lucaskkergg/proj_int_1_sem_2020_grupo_d_manut/Documentos/AULA-04-TORÇÃO.pdf

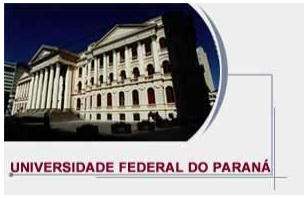
[picture p108: figure]

# TORÇÃO

Prof. Dr. Carlos A. Nadal

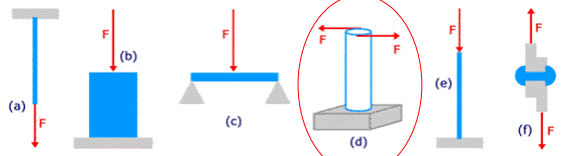
[picture p109: figure]

Tipo de esforços
a) Tração
b) Compressão
c) Flexão
d) Torção
e) Compressão
f) flambagem

Esforços axiais

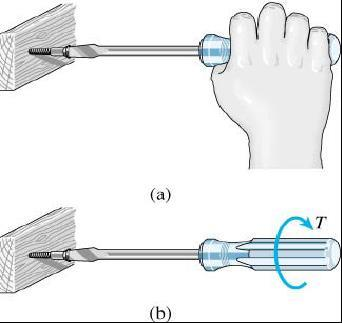
[picture p110: figure]

existe uma torção quando
uma seção transversal de
uma peça está sob a ação
de um conjugado que
tende a torce-la.

O plano de ação do conjugado = plano da seção transversal.
Os conjugados são chamados de momentos de torção, momentos torcionais ou torque T , ' T , e que têm a mesma intensidade T e sentidos opostos (Nash,1982).

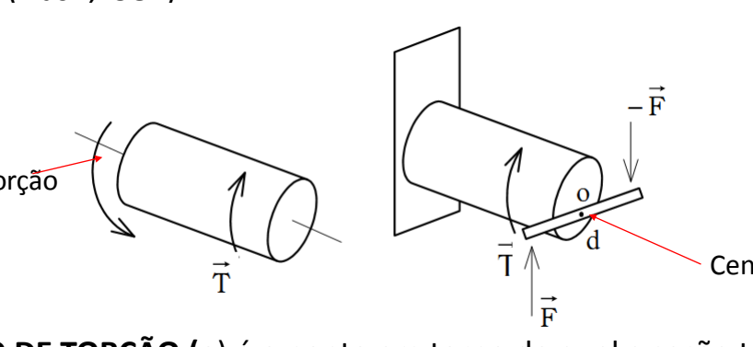
[picture p111: figure]

Centro de torção

Eixo de torção

CENTRO DE TORÇÃO (o) é o ponto em torno do qual a seção transversal gira. Para seções simétricas, coincide como o centro de gravidade.
EIXO DE TORÇÃO é o lugar geométrico dos centros de torção.

DEFORMAÇÕES NOS EIXOS CIRCULARES

Um eixo circular está fixado a um suporte por uma de suas extremidades e aplicando-se à extremidade livre um momento de torção T , o eixo gira, e a seção transversal da extremidade apresenta uma rotação representada pelo ângulo φ , chamado ângulo de torção (Beer and Johnston, 1989).

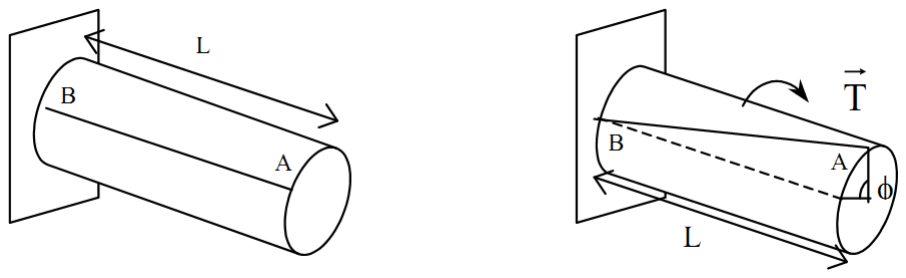
[picture p112: figure]

O ângulo de torção, para uma certa faixa de variação de T, é proporcional tanto a T como ao comprimento do eixo L.
Um prisma de seção circular, tendo uma de suas extremidades fixas, submetido a um momento de torção T.

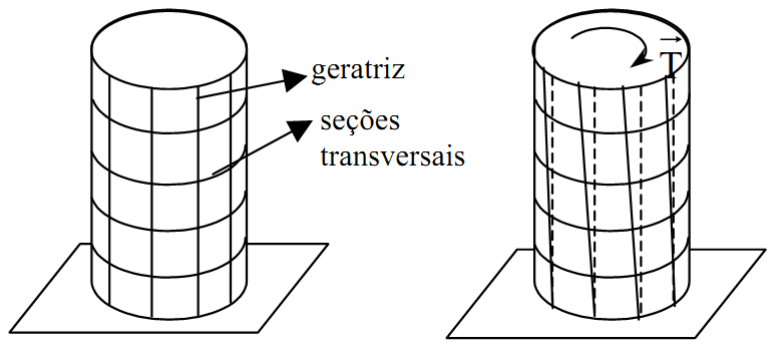
[picture p113: figure]

a) as geratrizes se transformam em hélices;
b) o “quadrado” se transforma em um “losango” com os lados sofrendo a mesma deformação angular;
c) as seções normais permanecem planas e normais ao eixo de rotação e conservam sua forma. Neste caso, é preciso assegurar que os momentos sejam aplicados de tal forma que as extremidades também permaneçam planas sem deformação.

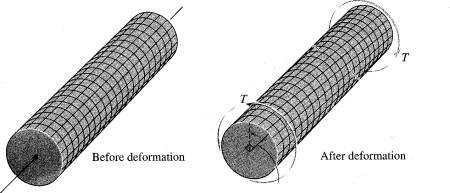
[picture p114: figure]
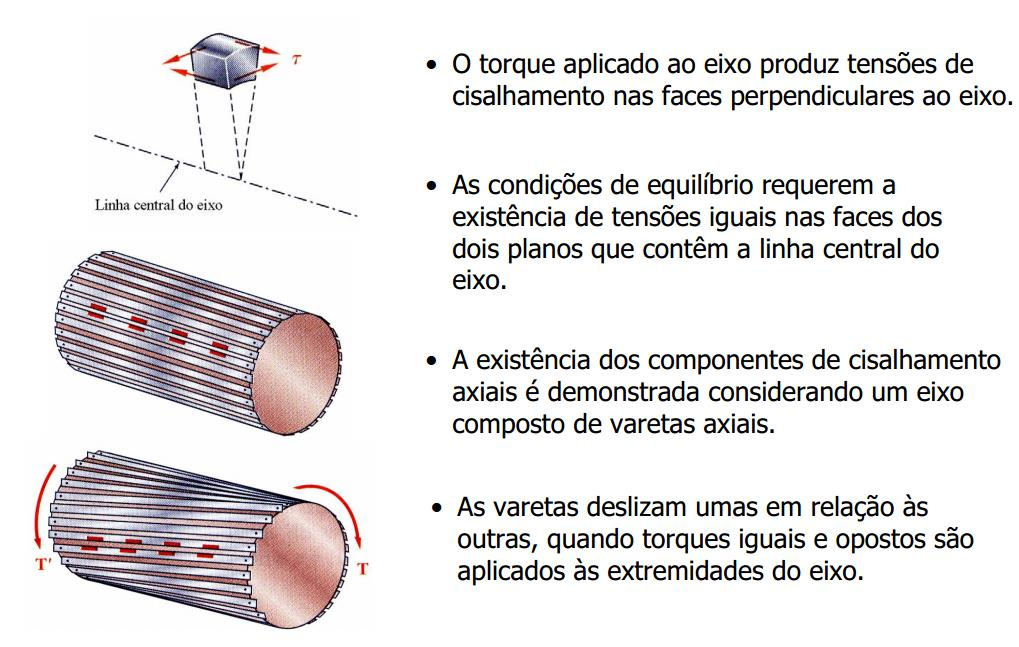
[picture p115: page 8]

Fonte: Prof. Renato Rocha – Resistência dos Materiais - UERJ

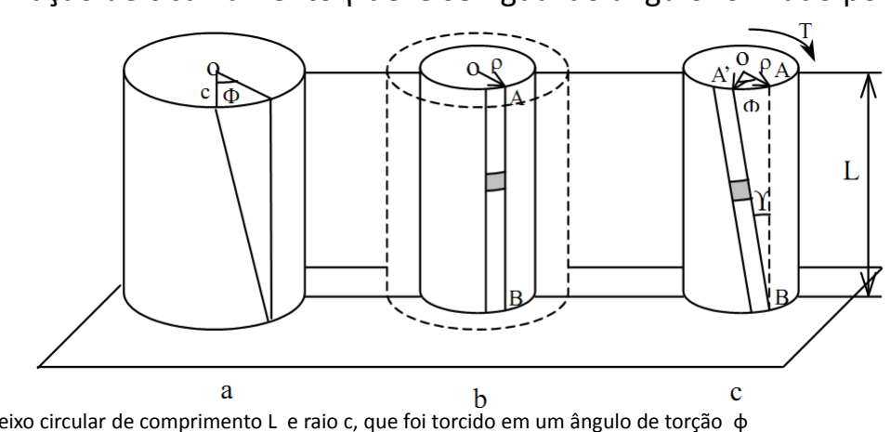
[picture p116: figure]

a) eixo circular de comprimento L e raio c, que foi torcido em um ângulo de torção φ
b) Retirando do interior do eixo um cilindro de raio ρ, marcando-se um “quadrado” sobre a superfície do mesmo, sem atuação de momento de torção.
c) Aplica-se a torção o “quadrado” se transforma em “losango”, as deformações de cisalhamento são medidas pela variação de dois lados;

Determinação da distribuição de tensões de cisalhamento na seção transversal deformação de cisalhamento γ deve ser igual ao ângulo formado por AB e A’B.

Pela figura observa-se que quando γ é pequeno, o comprimento de arco AA’ é dado por AA’=L.γ e na seção transversal AA’= ρ. φ

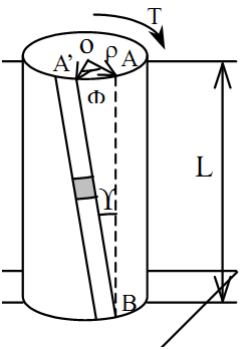
[picture p117: figure]

pode –se concluir que a deformação de cisalhamento em uma barra circular varia linearmente com a distância ao eixo da barra

g e r em radianos γ é máximo na superfície da barra circular, onde ρ = c

e

TENSÕES NO REGIME ELÁSTICO

Se a torção T tem um valor tal que as tensões no material se mantém abaixo da tensão de cisalhamento de escoamento τe.
Nesse caso, as tensões no material permanecem abaixo dos limites de proporcionalidade e elasticidade (Lei de Hooke)

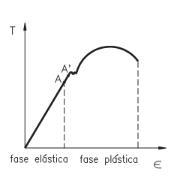
[picture p118: figure]

a tensão de cisalhamento na barra varia linearmente com a distância ρ do eixo da barra

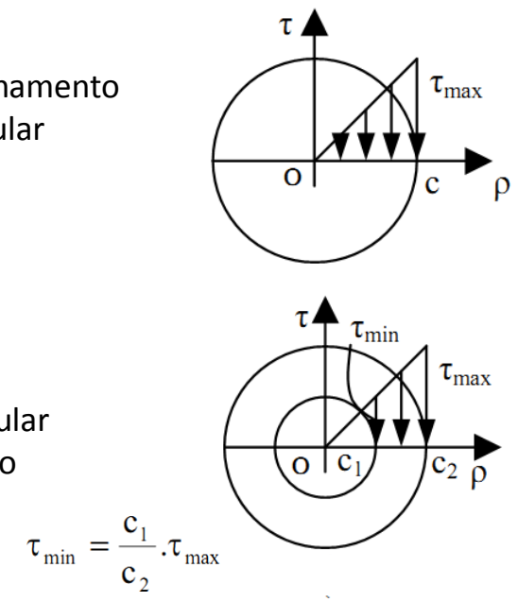
[picture p119: figure]

distribuição das tensões de cisalhamento na seção transversal de eixo circular maciço

distribuição das tensões de cisalhamento para um eixo circular vazado, de raio interno c1, e raio externo c2

Tensão máxima de torção

Tensão de cisalhamento a uma distância r do eixo da barra

momento de inércia polar de circulo de raio c

momento de inércia polar de um eixo circular de seção
vazada com raio interno c1 e raio externo c2.

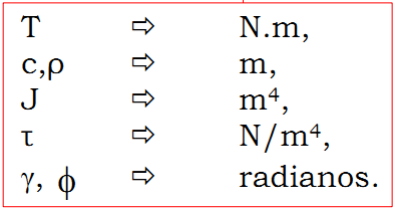
[picture p120: figure]

ÂNGULO DE TORÇÃO NO REGIME ELÁSTICO

eixo circular de comprimento L, seção transversal uniforme de raio c. O eixo está sujeito à ação de um momento de torção T.
O ângulo de torção φ e a deformação de cisalhamento máxima γmax estão relacionados por:

No regime elástico

e

φ é expresso radianos.
- No regime elástico, o ângulo de torção φ é proporcional ao momento de torção T aplicado no eixo circular.
- A equação só pode ser usada no caso de material homogêneo, para eixos de seção transversal constante e momentos aplicados nas
extremidades da barra.
- eixos submetidos a momentos de torção aplicados em outros pontos, com seções transversais compostas de materiais diferentes, ou seções transversais variáveis (divididos em várias partes), onde cada uma delas, individualmente, satisfaça as

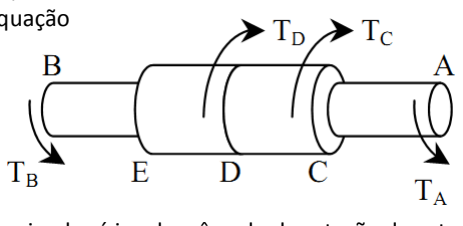
[picture p121: figure]

condições de emprego da equação

o ângulo de torção φ do eixo circular é igual ao ângulo de rotação da extremidade livre.

No caso do eixo AB, deve-se considerar quatro partes diferentes: AC,CD, DE e EB. O ângulo de torção total do eixo, isto é, o ângulo segundo o qual a seção A gira em relação a seção B, será obtido somando algebricamente os ângulos de torção de dada parte componente. Então o ângulo de torção total será dado por:

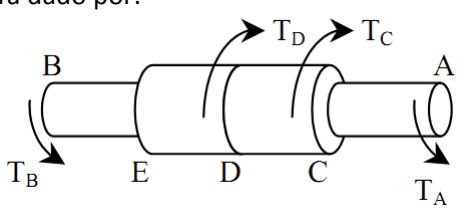
[picture p122: figure]

onde Ti, Li , Ji e Gi correspondem a parte i do eixo

Os eixos de transmissão podem ser maciços ou vazados.
A turbina A é conectada ao gerador B por meio do eixo de transmissão AB. Dividindo o conjunto nas três partes componentes, observa-se que a turbina exerce sobre o eixo um momento torcional ou torque T , e o eixo exerce sobre o gerador um torque de mesma intensidade. O gerador reage, exercendo sobre o eixo o momento torcional contrário T´

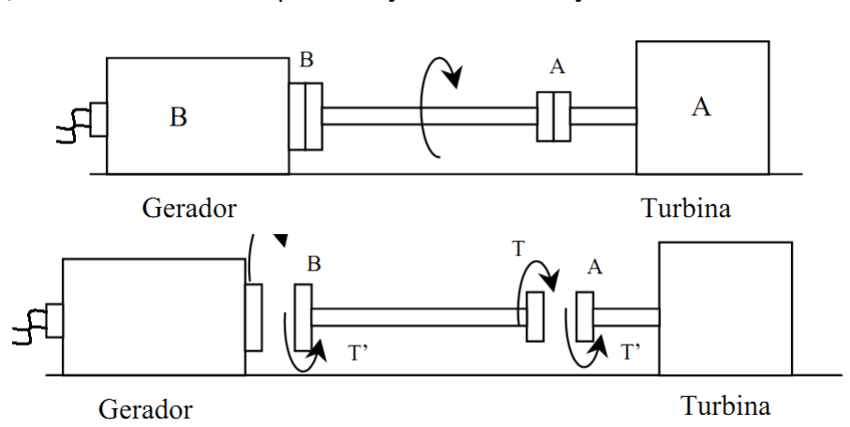
[picture p123: figure]

, da mesma maneira que a reação do eixo à ação da turbina é também o torque T´

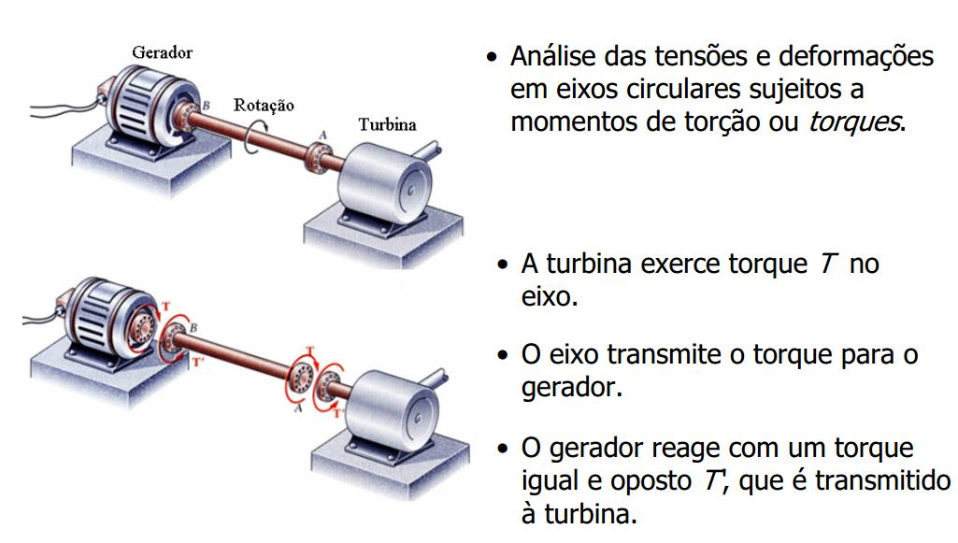
[picture p124: page 19]

Fonte: Prof. Renato Rocha – Resistência dos Materiais - UERJ

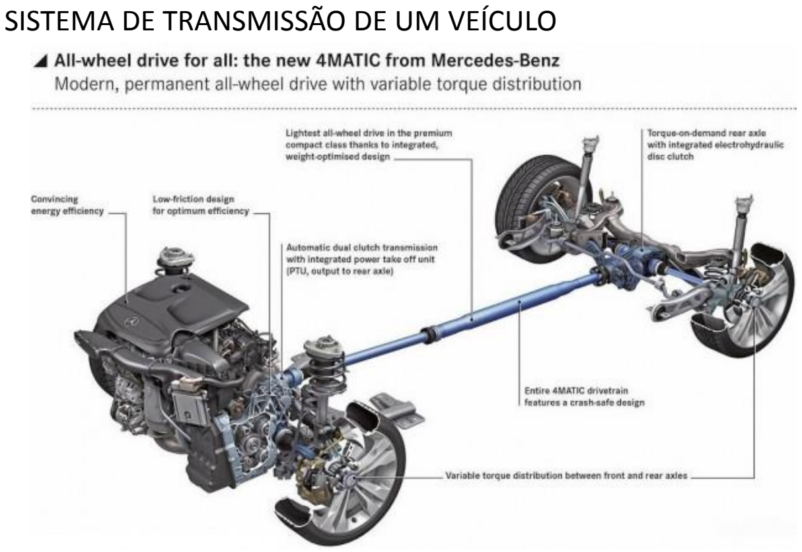
[picture p125: page 20]

SISTEMA DE TRANSMISSÃO DE UM VEÍCULO

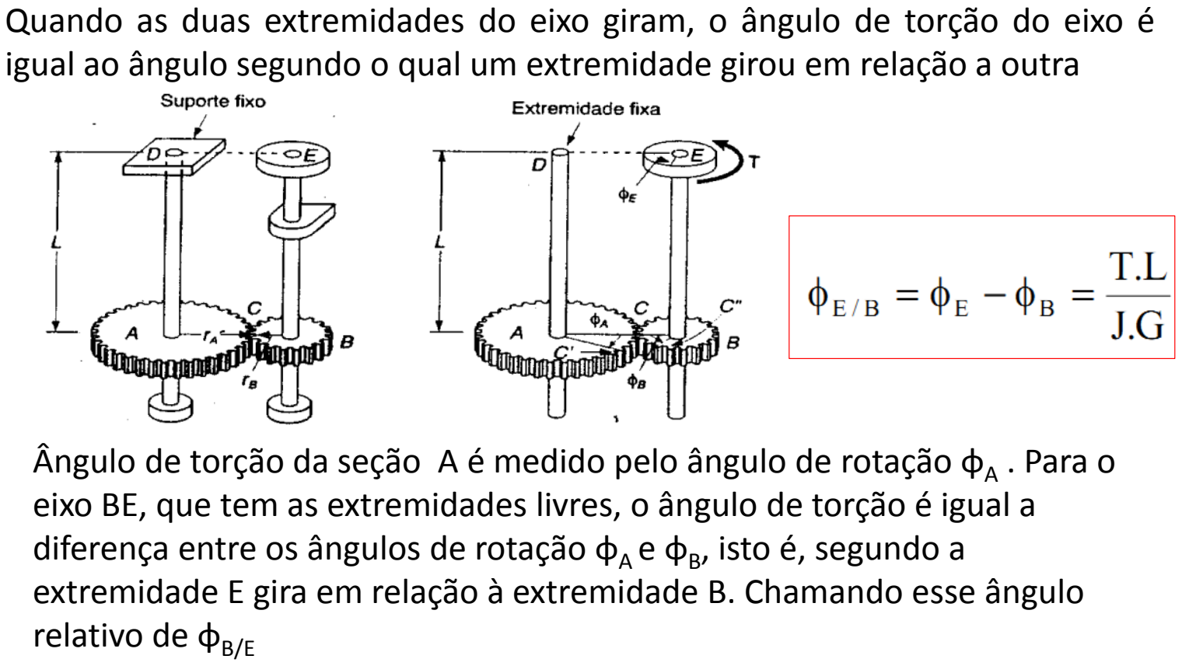
[picture p126: page 21]

Quando as duas extremidades do eixo giram, o ângulo de torção do eixo é igual ao ângulo segundo o qual um extremidade girou em relação a outra

Ângulo de torção da seção A é medido pelo ângulo de rotação φA . Para o
eixo BE, que tem as extremidades livres, o ângulo de torção é igual a diferença entre os ângulos de rotação φA e φB

, isto é, segundo a
extremidade E gira em relação à extremidade B. Chamando esse ângulo relativo de φB/E

Exemplo: No conjunto da figura, se rA=2.rB

, determinar o ângulo de rotação da extremidade do eixo BE, quando o momento de torção T é aplicado em E. Calculo do momento de torção TAD que atua no eixo AD.
No ponto de contato, C, das duas rodas dentadas ocorrem duas forças iguais e de sentido contrário, F e F' .
Sabe-se que rA=2.rB e TAD= 2.T, onde T é o momento de torção do eixo BE.

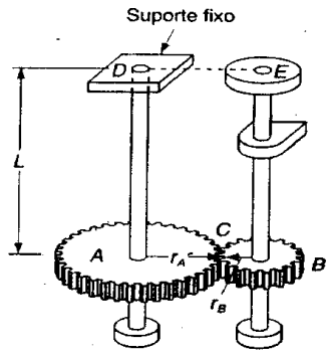
[picture p127: figure]
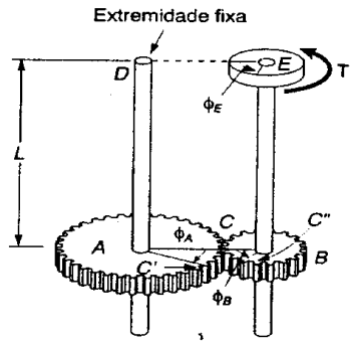
[picture p128: figure]
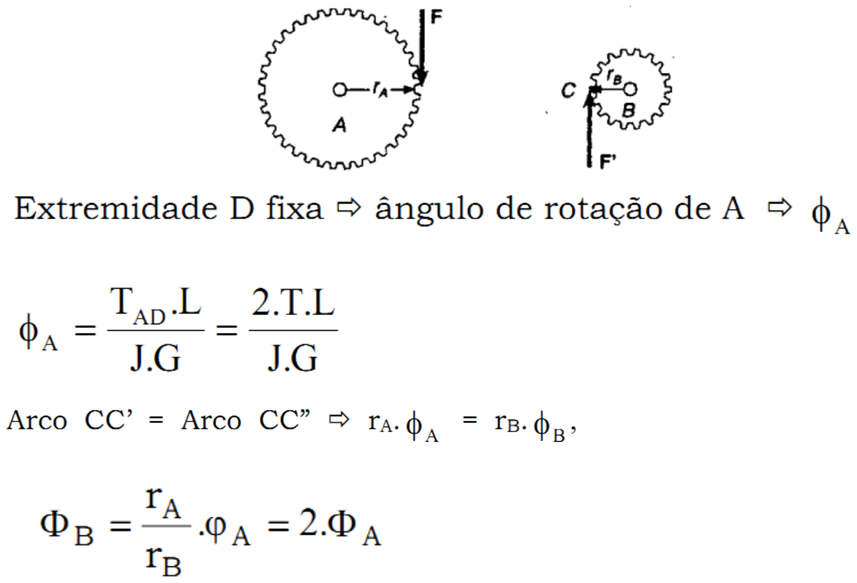
[picture p129: page 23]
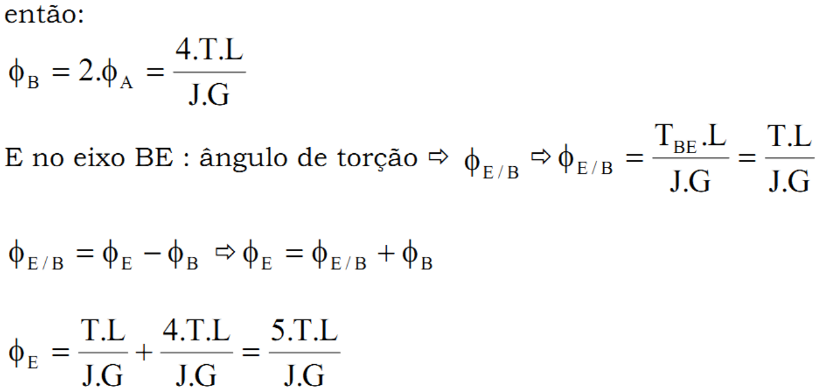
[picture p130: page 24]

TORÇÃO EM BARRAS DE SEÇÃO TRANSVERSAL NÃO CIRCULAR

As equações deduzidas nas seções anteriores, para a determinação das tensões e distribuição das deformações provocadas por carregamento torcional, são válidas para eixos de seção circular, e foi estabelecido que estas seções transversais permanecem planas após a deformação e mantêm sua forma.
Essa hipótese depende da assimetria da barra.
Em uma barra de seção transversal quadrada, quando submetida a uma torção, as suas diagonais bem como as linhas que ligam os pontos médios dos lados se conservam retas. Porém, qualquer outra linha se deformará quando a barra for torcida, devido a falta de assimetria, e a própria seção transversal sairá do seu plano original (Popov, 1976).

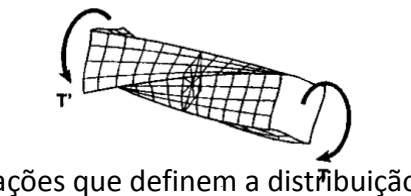
[picture p131: figure]

Deste modo, as equações que definem a distribuição de deformações e tensões em um eixo circular de material elástico, não podem ser usadas para seções não circulares. Assim, seria errado adotar uma barra de seção
quadrada, uma distribuição de tensões linear a partir do eixo da barra, variando com a distância ao centro da seção, que levassem a um máximo de tensões nos vértices do quadrado.
A determinação das tensões nas barras não circulares submetidas à torção, está além do alcance deste curso.
Por conveniência, indicam-se aqui alguns resultados da Teoria da Elasticidade, para o caso de barras de eixo reto, com seção retangular constante.

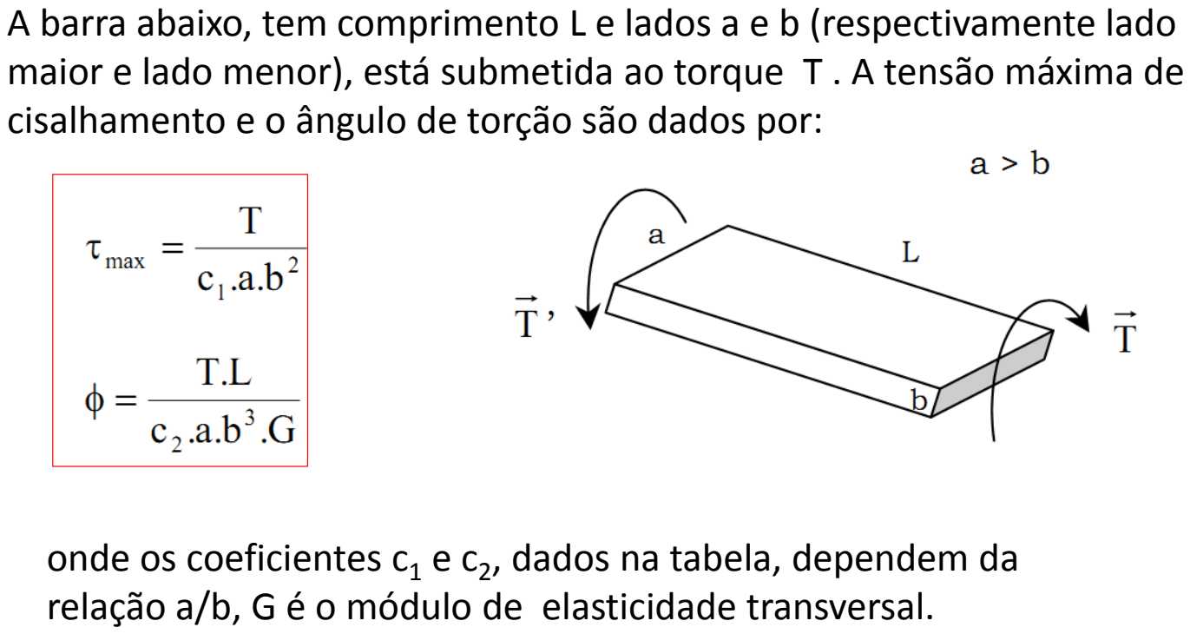
[picture p132: page 27]

A barra abaixo, tem comprimento L e lados a e b (respectivamente lado maior e lado menor), está submetida ao torque T . A tensão máxima de cisalhamento e o ângulo de torção são dados por:

onde os coeficientes c1 e c2

, dados na tabela, dependem da relação a/b, G é o módulo de elasticidade transversal.

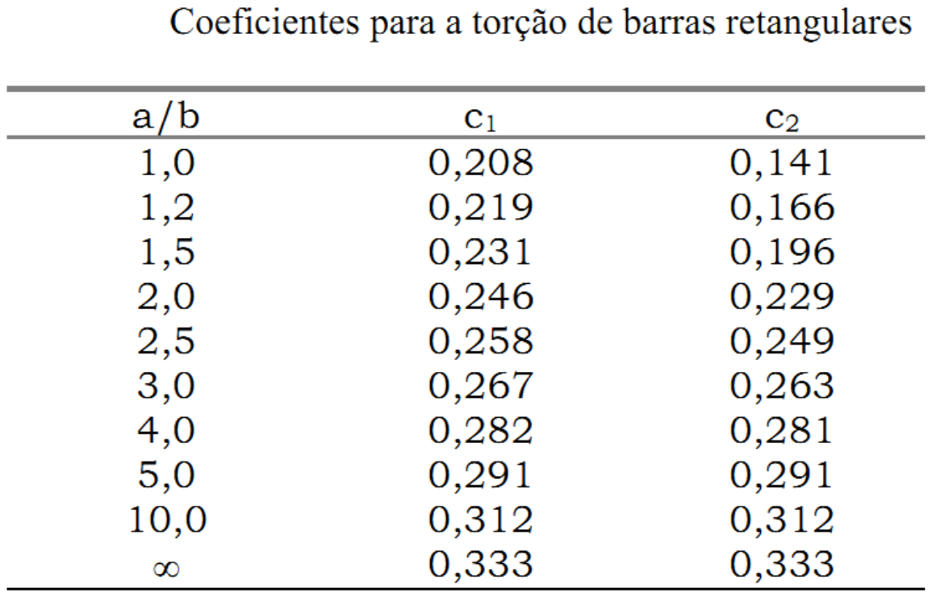
[picture p133: page 28]
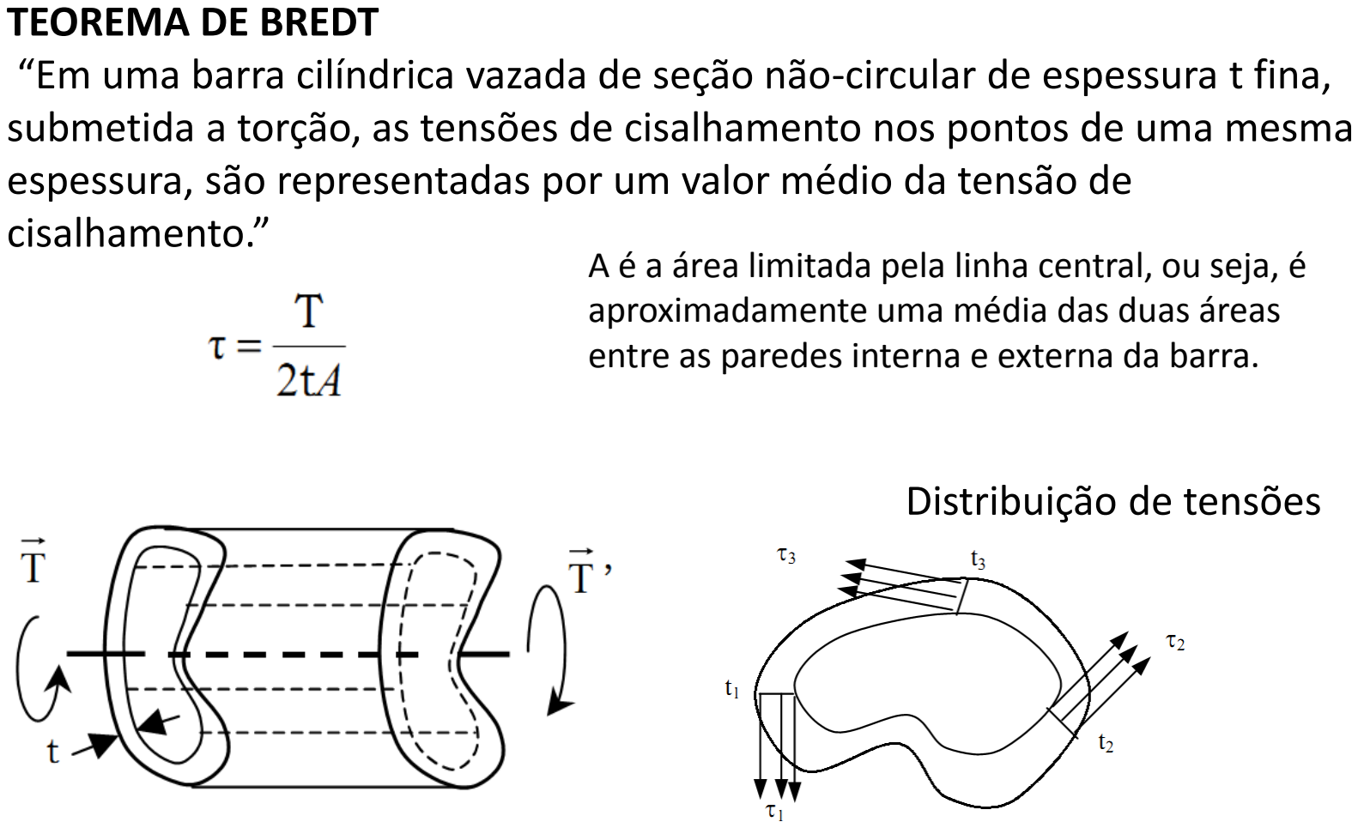
[picture p134: page 29]

TEOREMA DE BREDT
“Em uma barra cilíndrica vazada de seção não-circular de espessura t fina, submetida a torção, as tensões de cisalhamento nos pontos de uma mesma espessura, são representadas por um valor médio da tensão de cisalhamento.”

Distribuição de tensões

A é a área limitada pela linha central, ou seja, é aproximadamente uma média das duas áreas entre as paredes interna e externa da barra.

Fraturamento na Torção – resultados de ensaio

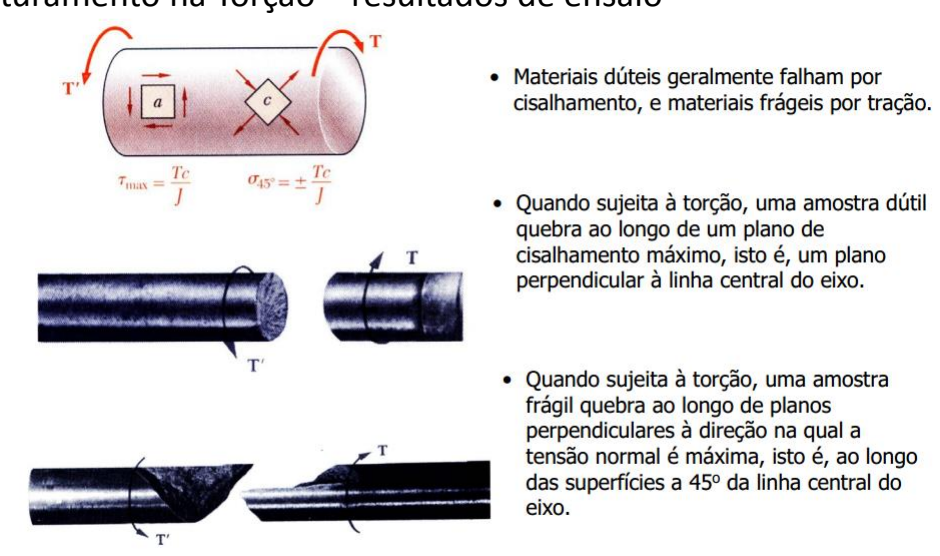
[picture p135: figure]

Fonte: Prof. Renato Rocha – Resistência dos Materiais - UERJ

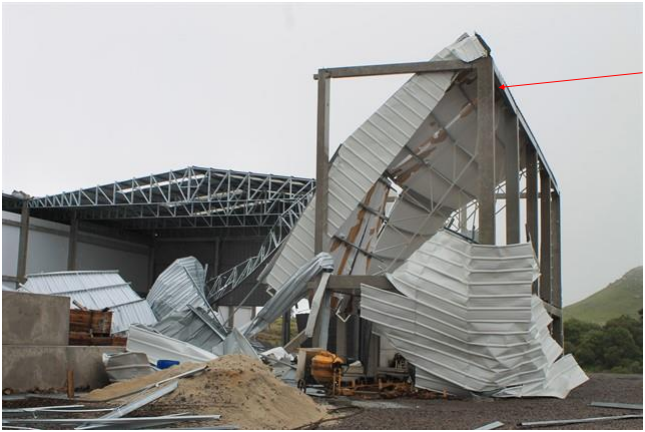
[picture p136: figure]

Onde está o efeito de torção nesta imagem?

Viga sujeita a
Torção
acidental

Ensaio de torção numa viga de concreto

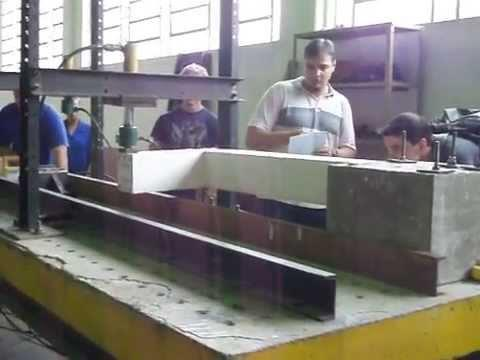
[picture p137: figure]
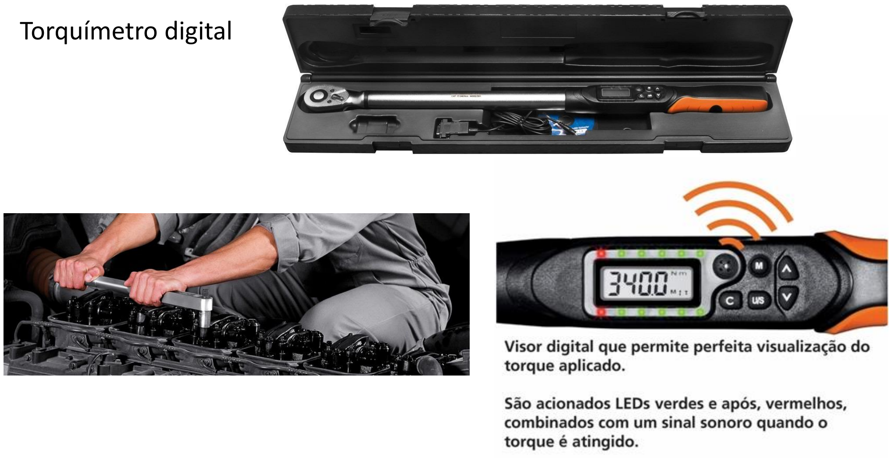
[picture p138: page 33]

Torquímetro digital

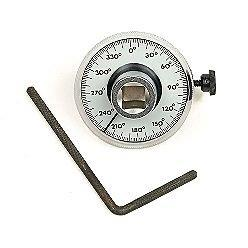
[picture p139: figure]
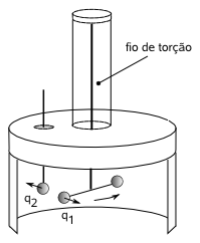
[picture p140: figure]

Medidor de ângulo de torque | Balança de torção
